LGenaroAlvarez/Hidroponia_automatica_2024_UVG/Documentos/trabajo_escrito_tesis_lgalvarez20168/0-datos_estudiante.tex

% ===============================================================================
% El estudiante debe llenar sus datos en esta sección para que la plantilla los 
% auto-importe y genere automáticamente las páginas de portada y de firmas 
% autorizadas.
% ===============================================================================
% Datos del estudiante:
% -------------------------------------------------------------------------------
% Nombre completo
\def \nombreestudiante {Luis Genaro Álvarez Sulecio}
% Carné
\def \uvgcarne {20168}
% Facultad
\def \uvgfacultad {Ingeniería}
% Carrera
\def \uvgcarrera {Ingeniería Mecatrónica}

% Datos del trabajo:
% -------------------------------------------------------------------------------
% Título completo
\def \titulotesis {Diseño e implementación de un sistema hidropónico automático de técnica NFT para el cultivo de cilantro en un contexto urbano}
% Año de entrega
\def \anoentrega {2024}
% Asesor
\def \nombreasesor {Ing. Pedro Joaquín Castillo Coronado}

% Datos del tribunal examinador:
% -------------------------------------------------------------------------------
% Nombre del primer examinador
\def \nombreprimerex {MSc. Carlos Esquit}
% Nombre del segundo examinador
\def \nombresegundoex {Ing. Luis Pedro Montenegro}
% Año de aprobación
\def \anoaprobacion {2021}
% Mes de aprobación
\def \mesaprobacion {diciembre }
% Día de aprobación
\def \diaaprobacion {5 }

% Capítulos pre-definidos
% -------------------------------------------------------------------------------
% Comentar las líneas de las secciones que desean omitirse, por defecto se 
% se incluyen todas.
\def \CAPprefacio {Prefacio}
\def \CAPantecedentes {Antecedentes}
\def \CAPalcance {Alcance}
\def \CAPanexos {Anexos}
\def \CAPglosario {Glosario}

% Formato y estilo de la plantilla
% -------------------------------------------------------------------------------
% Modo impresión: Puede des-comentar la siguiente línea para generar un documento pdf sin la portada, para cuando se desee imprimir el documento para encuadernación
% \def \printver {Versión del documento para impresión}

% Portada: Puede cambiarse la imagen en la portada al cambiar el nombre del 
% archivo siguiente. NOTA: debe tener la suficiente resolución para cubrir el área
% designada
\def \imagenportada {plantilla/portadacit.jpg}

% Referencias: Puede des-comentar la siguiente línea para utilizar el formato de referencias APA
%\def \usarAPA {Usar formato APA}

% Párrafo: Puede comentar la siguiente línea si desea emplear un formato de 
% párrafo distinto al establecido por defecto
\def \parpordefecto {Formato de párrafo por defecto}

% Capítulos y secciones: Puede des-comentar la siguiente línea para establecer el
% formato de los capítulos y secciones bajo el estándar original de UVG para
% trabajos de graduación. Este incluye: capítulos con numeración romana, secciones
% con letras mayúsculas, sub-secciones con números y sub-sub-secciones con letras
% minúsculas
%\def \capsecuvg {Formato UVG para capítulos y secciones}
