LGenaroAlvarez/Hidroponia_automatica_2024_UVG/Documentos/trabajo_escrito_tesis_lgalvarez20168/g-objetivos.tex

\section{Objetivo General}
Diseñar e implementar un sistema hidropónico automático capaz de mantener una producción de hortalizas en un contexto urbano con espacio reducido.

\section{Objetivos específicos}
\begin{itemize}
	\item Diseñar e implementar un sistema hidropónico automático de dimensiones compactas con monitoreo y regulación de parámetros del agua. 
	\item Comparar las características de crecimiento del cilantro en el sistema hidropónico automático contra una metodología tradicional.
	\item Integrar el sistema hidropónico automático con una aplicación móvil para un monitoreo remoto de parámetros.
\end{itemize}
