LGenaroAlvarez/Hidroponia_automatica_2024_UVG/Documentos/trabajo_escrito_tesis_lgalvarez20168/l-recomendaciones.tex

A lo largo de las diferentes etapas de desarrollo de este proyecto de graduación, se identificaron diferentes características que se deben considerar a la hora de continuar con el desarrollo del sistema. Si bien estas características no afectaron directamente el funcionamiento principal del sistema, se consideró que su implementación facilitaría considerablemente el proceso de desarrollo, construcción, y resultados finales del trabajo. A continuación se encuentra un listado de las recomendaciones principales del presente trabajo de graduación.

\begin{itemize}
	\item Emplear una combinación de dos microcontroladores, dedicando uno al análisis y manejo de datos y el segundo a el control de sensores y actuadores con tal de reducir la carga del firmware sobre el microcontrolador.
	\item Utilizar un sistema de ventilación más robusto que asegure un mejor flujo de aire y permita regular la temperatura del sistema tanto para enfriar como para calentar el entorno.
\end{itemize}
