LGenaroAlvarez/Hidroponia_automatica_2024_UVG/Documentos/plantilla-protocolo-uvg-2020-v1/q-cronograma.tex

\begin{figure}[H]
	\centering
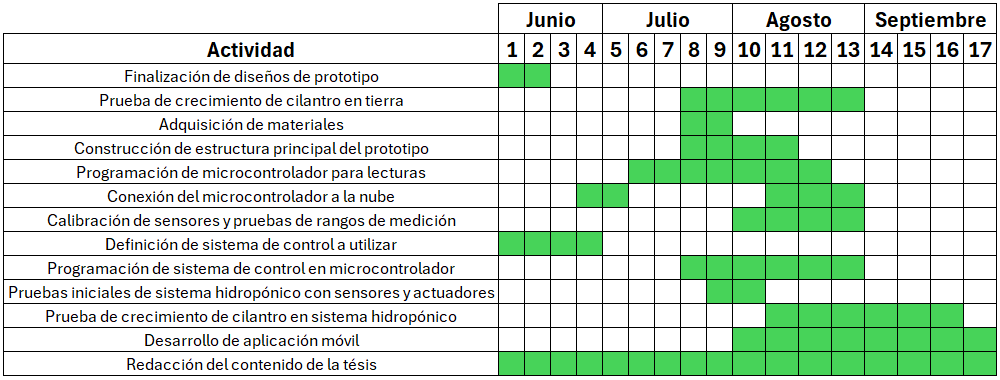
[picture p35: Documentos/plantilla-protocolo-uvg-2020-v1/figuras/Cronograma_actividades1.png]
	
	\caption{Cronograma de actividades para segundo ciclo.}
	\label{fig1}
\end{figure}
