LGenaroAlvarez/Hidroponia_automatica_2024_UVG/Desarrollo PCB/TH_pcb_TL.png

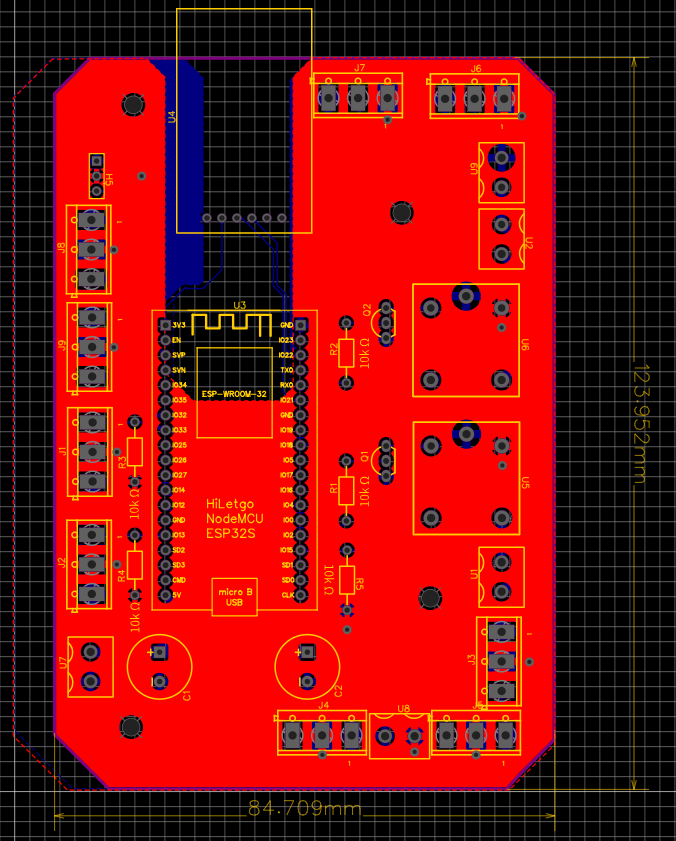
Desarrollo PCB/TH_pcb_TL.png
