LGenaroAlvarez/Hidroponia_automatica_2024_UVG/Documentos/trabajo_escrito_tesis_lgalvarez20168/figuras/Cronograma_actividades.png

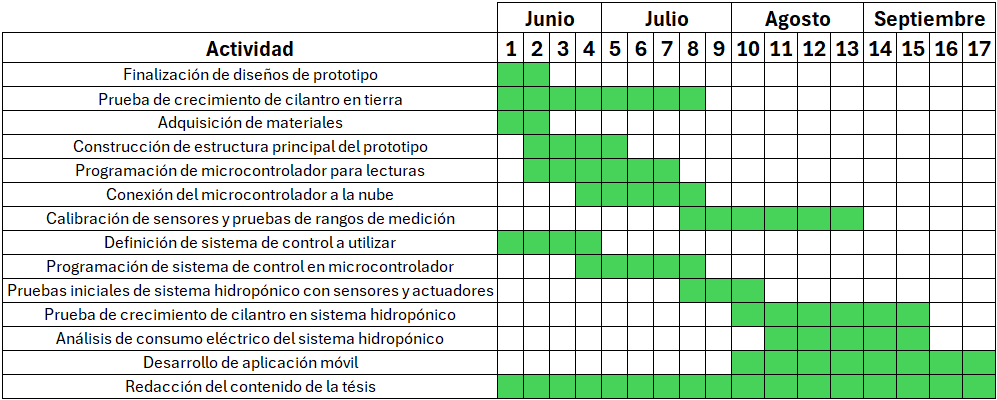
Documentos/trabajo_escrito_tesis_lgalvarez20168/figuras/Cronograma_actividades.png
