LGenaroAlvarez/Hidroponia_automatica_2024_UVG/Documentos/trabajo_escrito_tesis_lgalvarez20168/figuras/Figura_12_esp32_doit.png

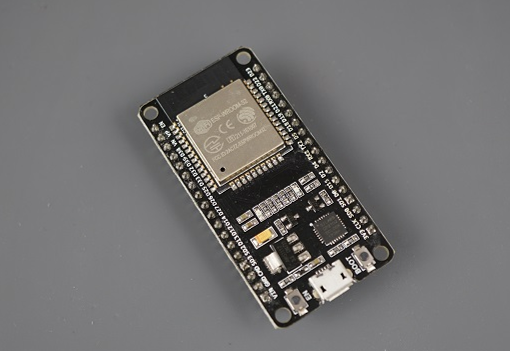
Documentos/trabajo_escrito_tesis_lgalvarez20168/figuras/Figura_12_esp32_doit.png
