LGenaroAlvarez/Hidroponia_automatica_2024_UVG/Documentos/trabajo_escrito_tesis_lgalvarez20168/figuras/Historico_temperatura_ambiente_12-octubre.png

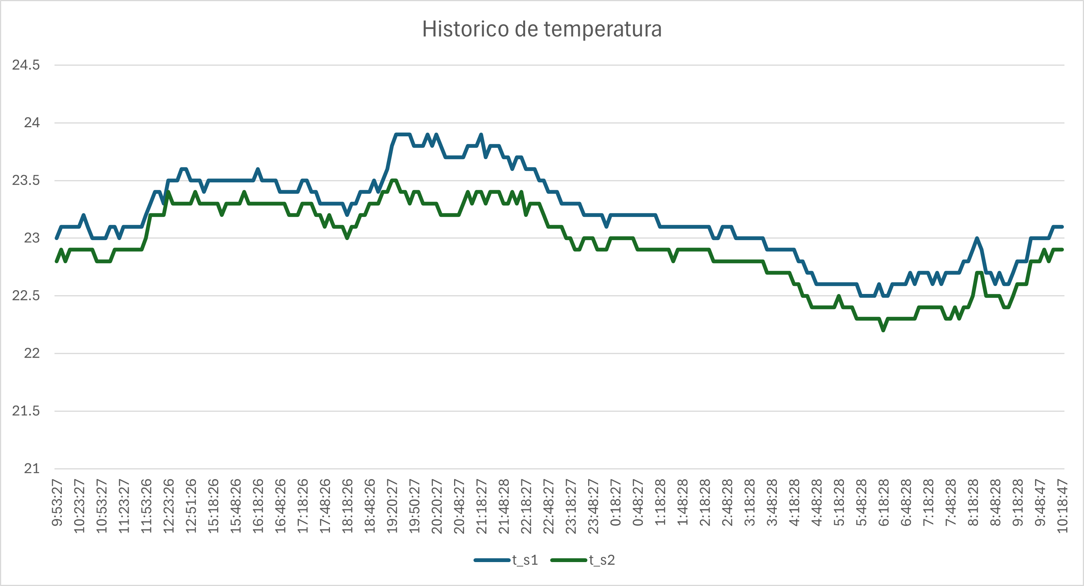
Documentos/trabajo_escrito_tesis_lgalvarez20168/figuras/Historico_temperatura_ambiente_12-octubre.png
